Reemuson/MENG4210-Assignment-1/HTML/images/cat_png_3d_viewer_bottom_Input-Protection-bottom.png

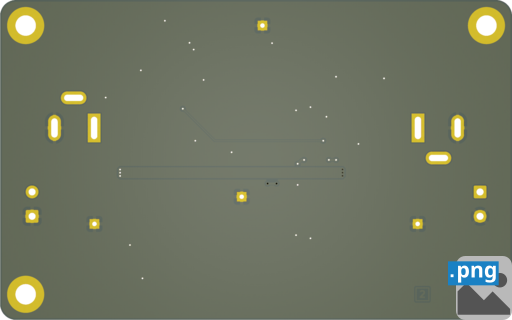
HTML/images/cat_png_3d_viewer_bottom_Input-Protection-bottom.png
