Reemuson/MENG4210-Assignment-1/HTML/images/cat_pdf_assembly_Input-Protection-assembly.png

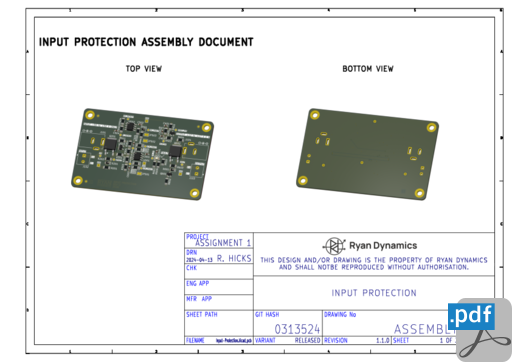
HTML/images/cat_pdf_assembly_Input-Protection-assembly.png
